sebasack/v-plotter/circuitos/2240466265006.jpg

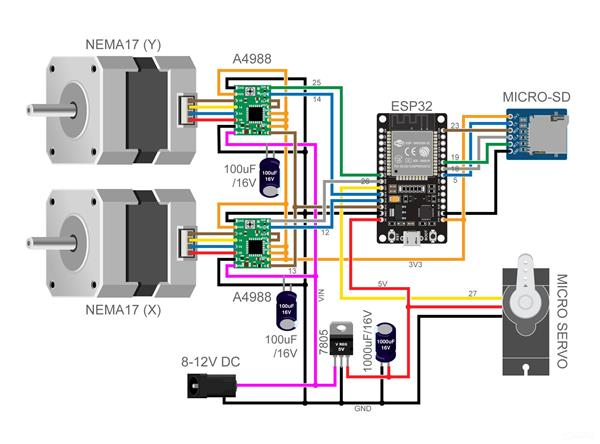
circuitos/2240466265006.jpg
