sebasack/v-plotter/circuitos/ESP32-interfacing-circuit-with-28BYJ-48-stepper-motor-and-uln2007.jpg

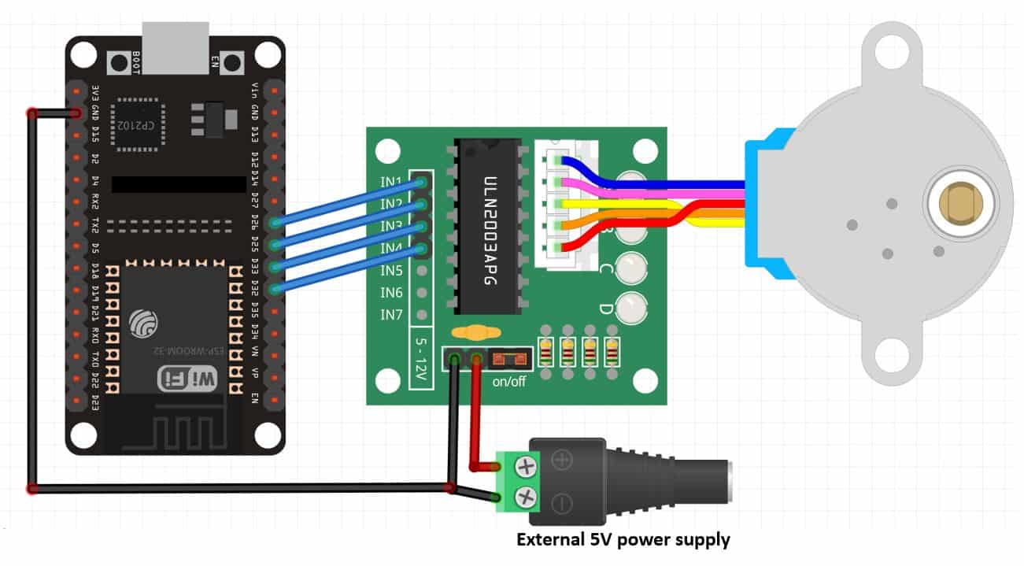
circuitos/ESP32-interfacing-circuit-with-28BYJ-48-stepper-motor-and-uln2007.jpg
