sebasack/v-plotter/convertir/pde/outline/outline_image.jpg

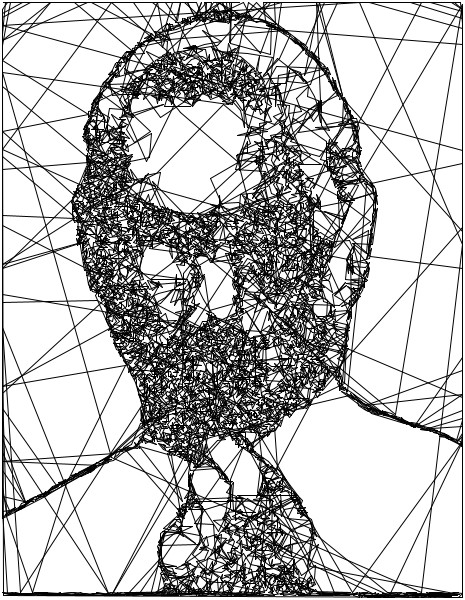
convertir/pde/outline/outline_image.jpg
