sebasack/v-plotter/hardware/mdf/Sde6bad2016fb44128df59bd70b1d3508Q.webp

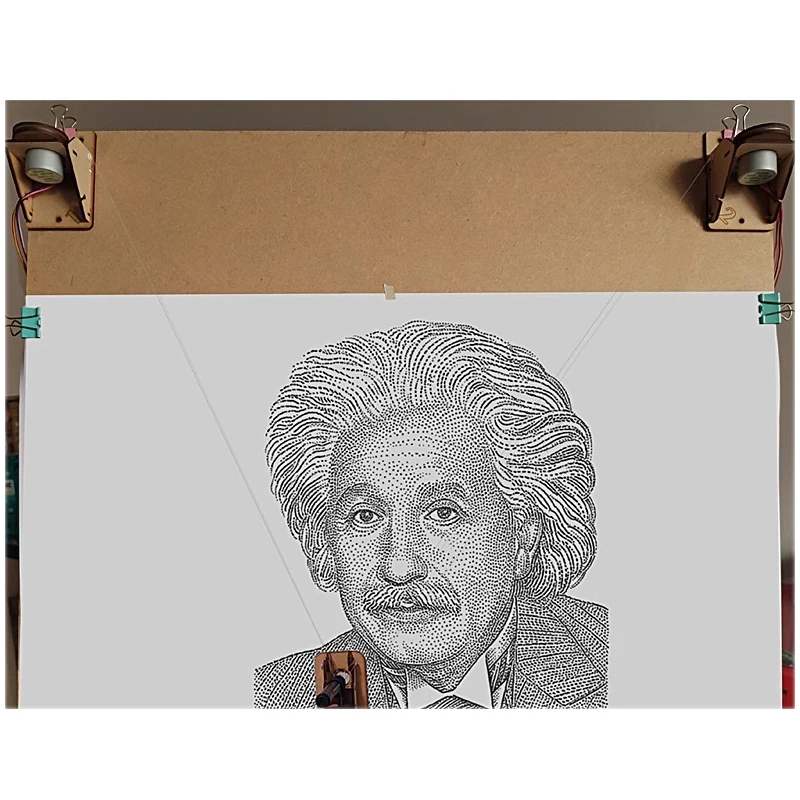
hardware/mdf/Sde6bad2016fb44128df59bd70b1d3508Q.webp
