sebasack/v-plotter/imagenes/bird.jpg

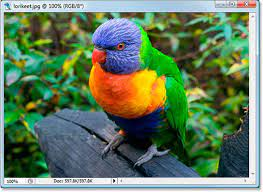
imagenes/bird.jpg
