sebasack/v-plotter/imagenes/casa.jpg

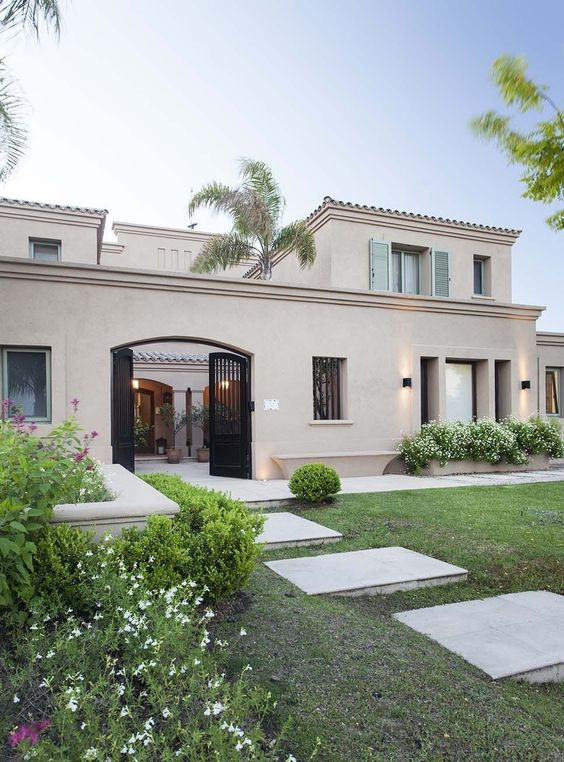
imagenes/casa.jpg
