sebasack/v-plotter/imagenes/cat.png

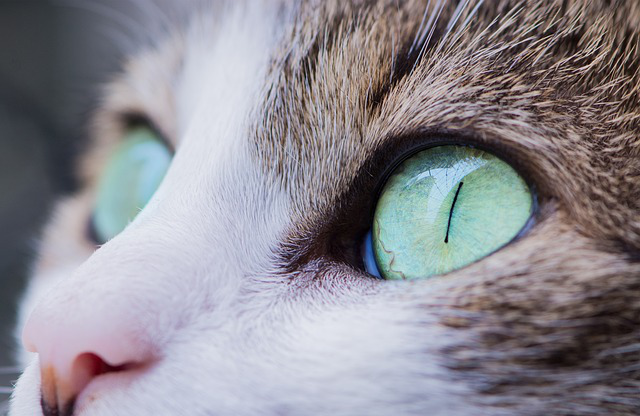
imagenes/cat.png
