sebasack/v-plotter/imagenes/dog.jpg

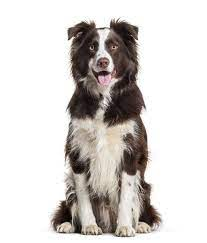
imagenes/dog.jpg
