sebasack/v-plotter/imagenes/escritorio.png

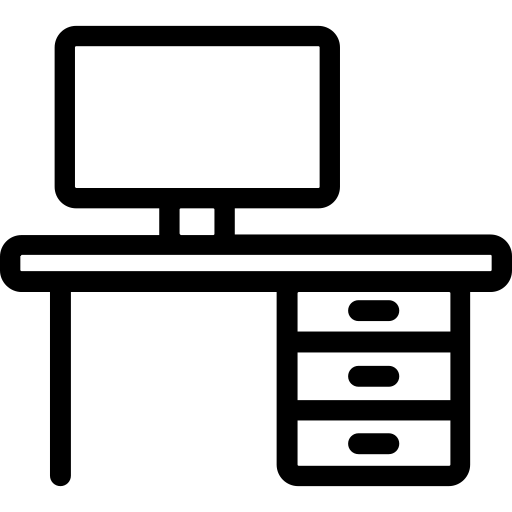
imagenes/escritorio.png
