sebasack/v-plotter/imagenes/figuras.webp

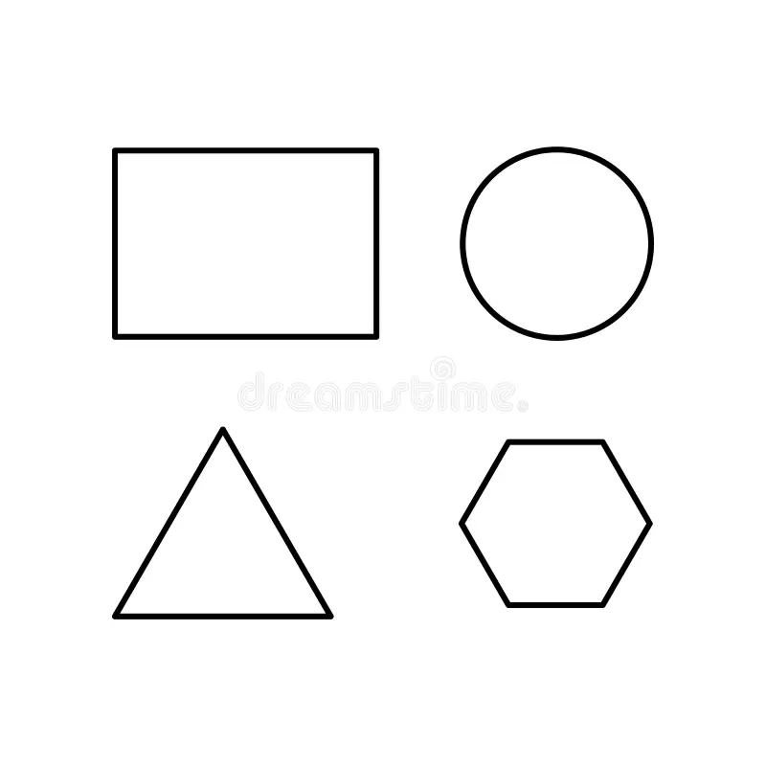
imagenes/figuras.webp
