sebasack/v-plotter/imagenes/jeep-wagoneer-2021.jpg

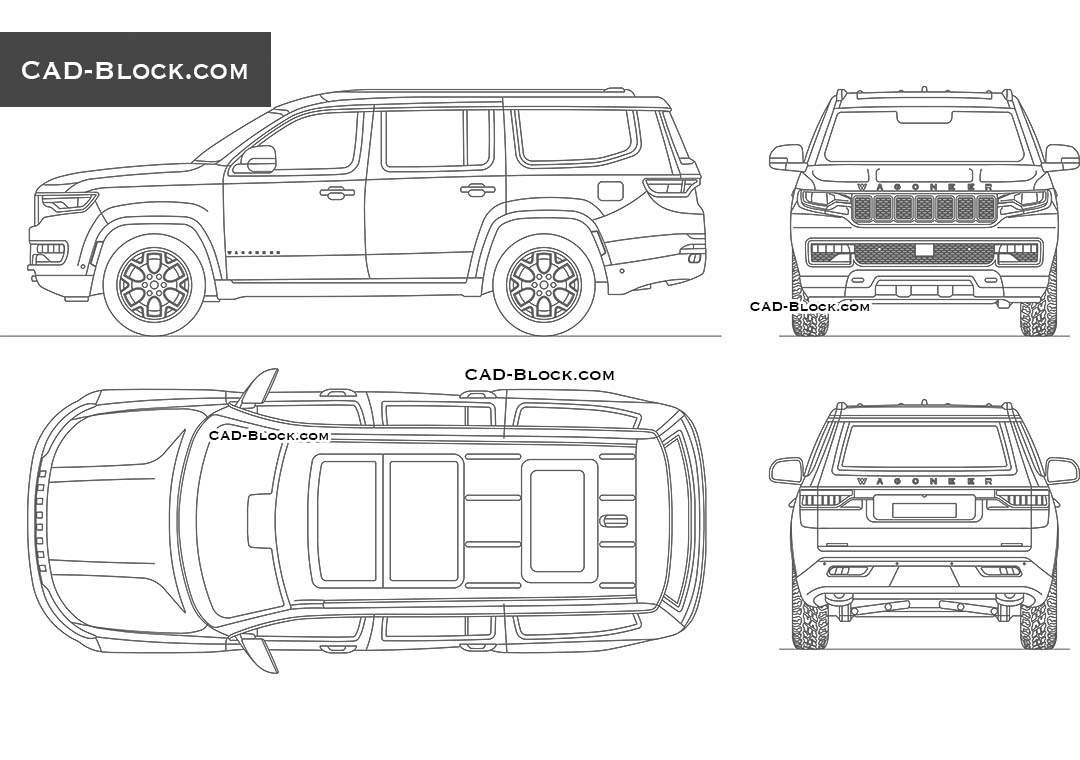
imagenes/jeep-wagoneer-2021.jpg
