sebasack/v-plotter/imagenes/manzana.jpg

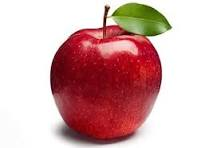
imagenes/manzana.jpg
