sebasack/v-plotter/imagenes/mariposa.jpg

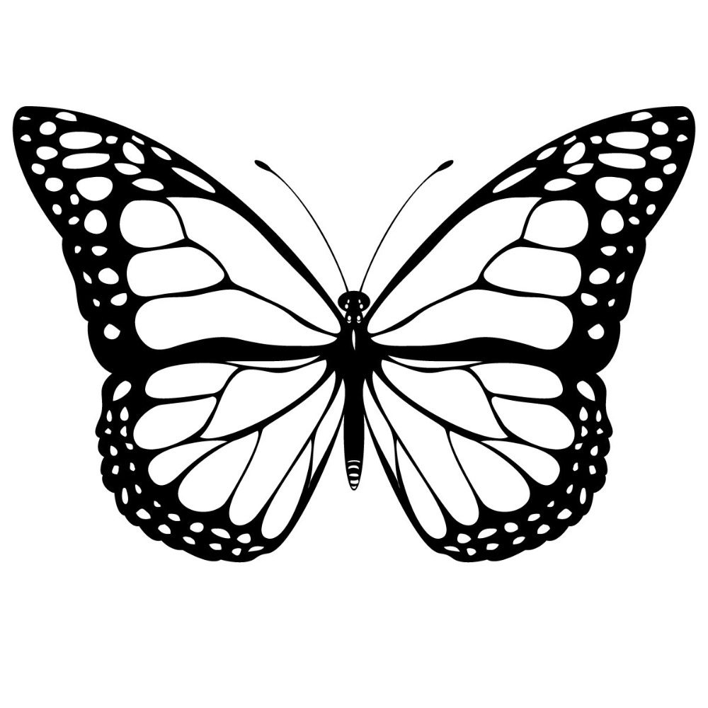
imagenes/mariposa.jpg
