sebasack/v-plotter/imagenes/mariposa_chica.jpg

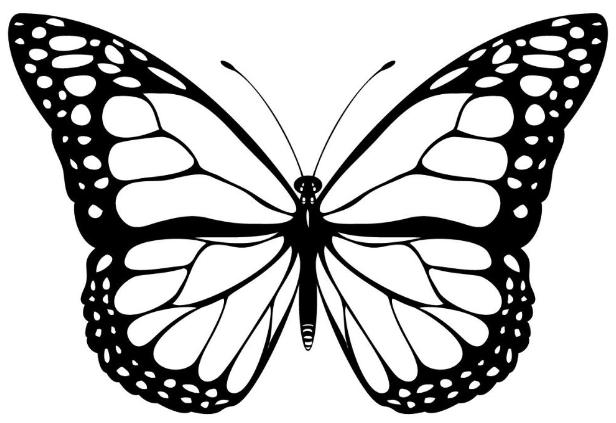
imagenes/mariposa_chica.jpg
