sebasack/v-plotter/imagenes/mariposa_inv.jpg

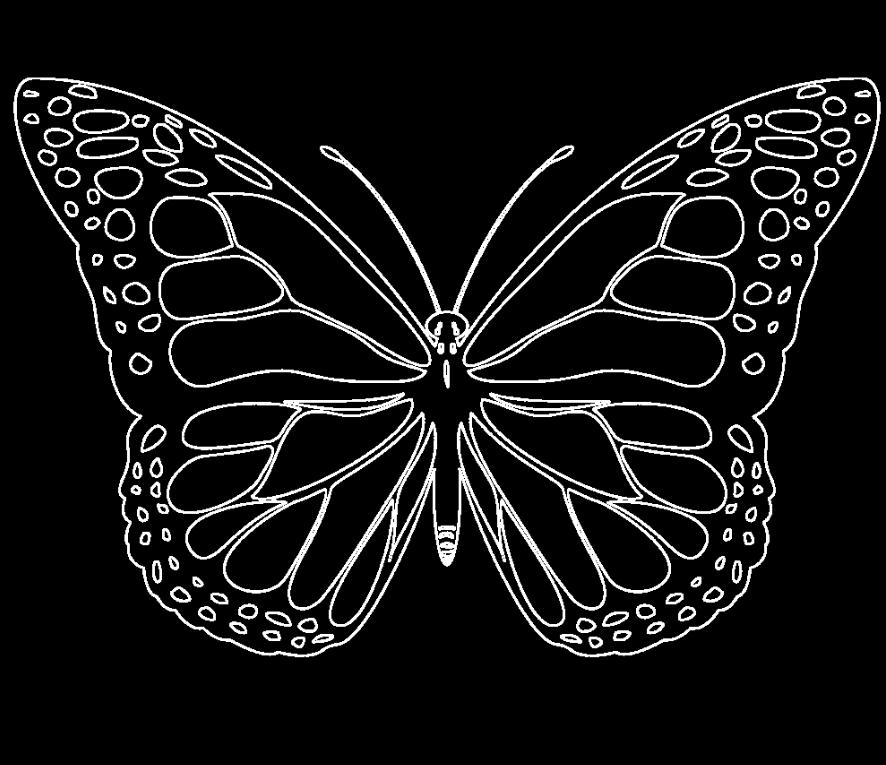
imagenes/mariposa_inv.jpg
