sebasack/v-plotter/imagenes/mariposas.jpg

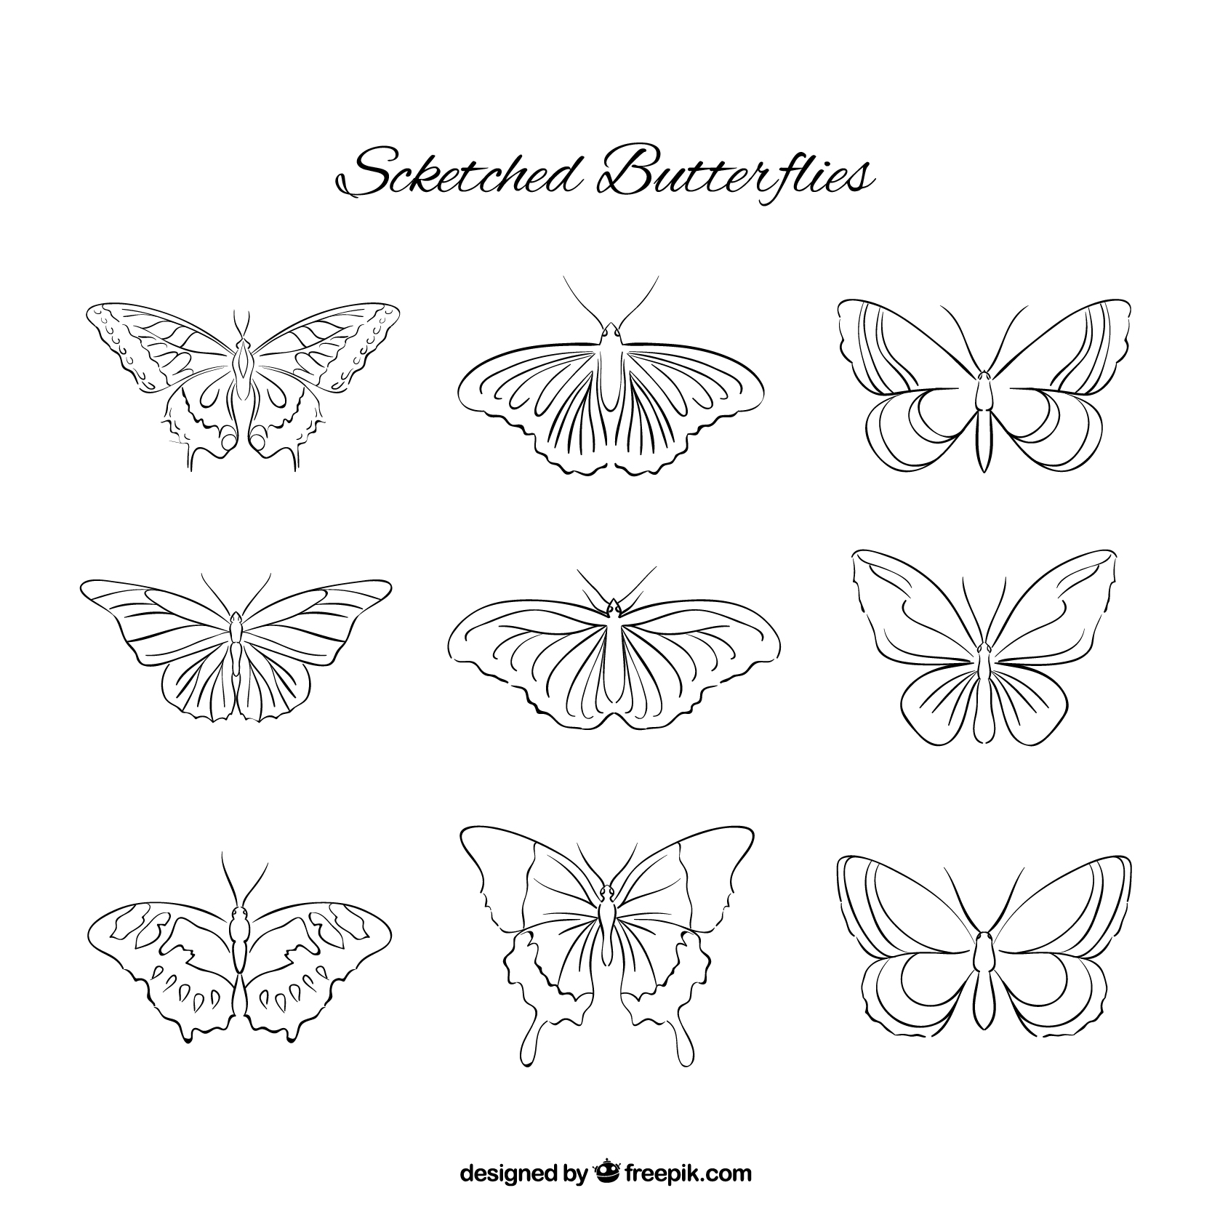
imagenes/mariposas.jpg
