sebasack/v-plotter/imagenes/nano-banana-2025-10-07T18-07-37.png

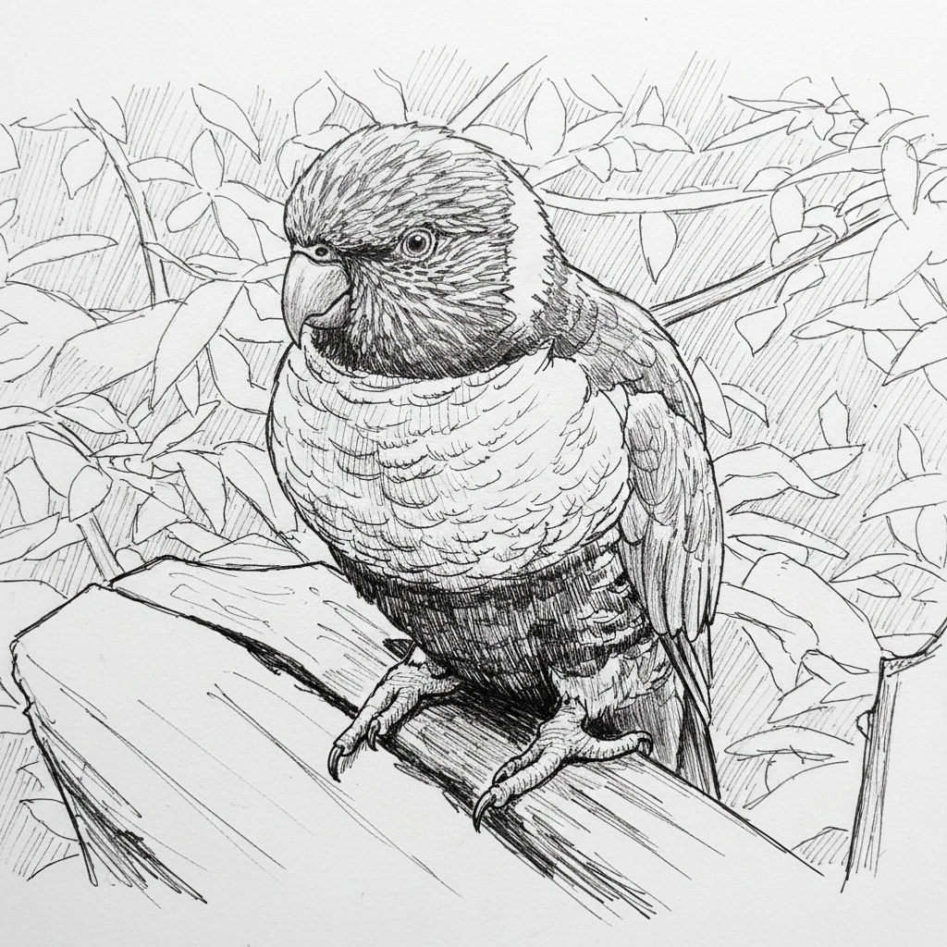
imagenes/nano-banana-2025-10-07T18-07-37.png
