sebasack/v-plotter/imagenes/perrito.jpg

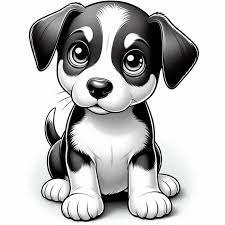
imagenes/perrito.jpg
