sebasack/v-plotter/imagenes/rgb-cmyk-modos-color.png

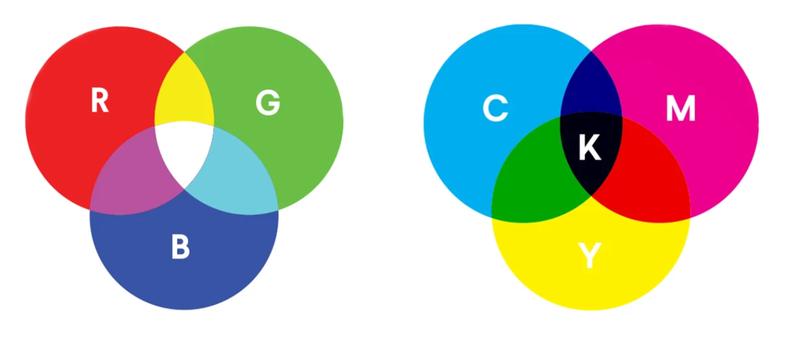
imagenes/rgb-cmyk-modos-color.png
