sebasack/v-plotter/SD/vPlotterMap.png

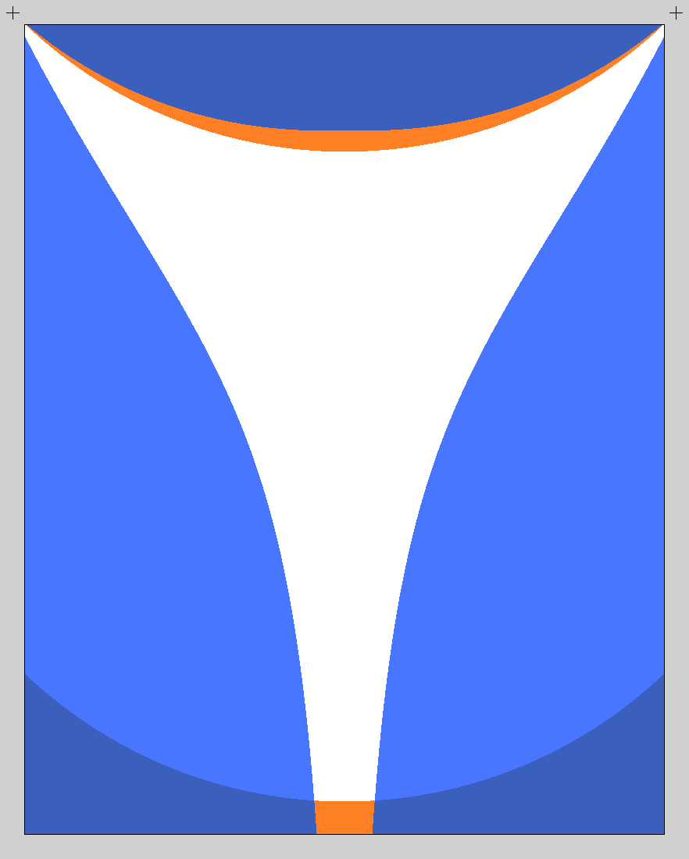
SD/vPlotterMap.png
