sebasack/v-plotter/v-plotter/util.ino

/**
*  Polargraph Server. - CORE
*  Written by Sandy Noble
*  Released under GNU License version 3.
*  http://www.polargraph.co.uk
*  https://github.com/euphy/polargraph_server_polarshield

Util.

This is one of the core files for the polargraph server program.

This has all the methods that let the rest actually work, including
the geometry routines that convert from the different coordinates
systems, and do transformations.
*/

static float translateX = 0.0;
static float translateY = 0.0;
static float scaleX = 1.0;
static float scaleY = 1.0;
static int rotateTransform = 0;

long multiplier(int in){
  return multiplier(long(in));
}

long multiplier(long in){
  return in * long(stepMultiplier);
}

float multiplier(double in){
  float out = in * (float) stepMultiplier;
  return out;
}

long divider(long in){
  return in / float(stepMultiplier);
}

void transform(long &tA, long &tB){

  tA = tA * scaleX;
  tB = tB * scaleY;

  // rotate

  if (rotateTransform >45 && rotateTransform <= 135){// 90 degree rotation
  
    float temp = tA;
    tA = -tB;
    tB = temp;
  } else if (rotateTransform > 135 && rotateTransform <= 225){// 180 degree rotation
  
    tA = -tA;
    tB = -tB;
  } else if (rotateTransform > 225 && rotateTransform <= 315){// 270 degree rotation
  
    float temp = tA;
    tA = tB;
    tB = -temp;
  } else {// no rotation  

  }

  tA = tA + translateX;
  tB = tB + translateY;

//  Serial.print("Out tA:");
//  Serial.println(tA);
//  Serial.print("Out tB:");
//  Serial.println(tB);

}

void changeLength(float tA, float tB){
  changeLength((long)tA, (long)tB);
}

void changeLength(long tA, long tB){
// Here. Finally. the motor moves.  CMD_CHANGELENGTHDIRECT = "C17" eventually gets here

  transform(tA,tB);

  float currSpeedA = motorA.speed();
  float currSpeedB = motorB.speed();

  // Serial.printf("A pos: %ld, A target: %ld\n", motorA.currentPosition(), tA);
  // Serial.printf("B pos: %ld, B target: %ld\n", motorB.currentPosition(), tB);


  motorA.setSpeed(0.0);
  motorB.setSpeed(0.0);
  motorA.moveTo(tA);
  motorB.moveTo(tB);

  if (!usingAcceleration)  {
    // The moveTo() function changes the speed in order to do a proper
    // acceleration. This counteracts it. Ha.
    
    if (motorA.speed() < 0){
      currSpeedA = -currSpeedA;
     } 
    if (motorB.speed() < 0){
      currSpeedB = -currSpeedB;
      }

  //  Serial.printf("Setting A speed (%ld) back to %ld\n", motorA.speed(), currSpeedA);
  //  Serial.printf("Setting B speed (%ld) back to %ld\n", motorB.speed(), currSpeedB);
      
    motorA.setSpeed(currSpeedA);
    motorB.setSpeed(currSpeedB);
  }
  
  
  while (motorA.distanceToGo() != 0 || motorB.distanceToGo() != 0){
    // seemed like a good idea?  This loop will take some time to run...
    // no, not really
    // taskYIELD();

    // the motor moves here

//    Serial.print("dA:");
//    Serial.print(motorA.distanceToGo());
//    Serial.print(", dB:");
//    Serial.println(motorB.distanceToGo());
    // impl_runBackgroundProcesses();
    if (currentlyRunning){
      if (usingAcceleration){
        motorA.run();
        motorB.run();
      } else {
       // Serial.println(motorA.speed());

        motorA.runSpeedToPosition();
        motorB.runSpeedToPosition();
      }


     //   Serial.print(" mueve motor 1");
    }
//    } else {
//      impl_runBackgroundProcesses();    // it's already running as a task, why call it again?
//    }


  }

  lastOperationTime = millis();
  //reportPosition();
}

void changeLengthRelative(float tA, float tB){
  changeLengthRelative((long) tA, (long)tB);
}

void changeLengthRelative(long tA, long tB){
  motorA.move(tA);
  motorB.move(tB);

  while (motorA.distanceToGo() != 0 || motorB.distanceToGo() != 0)  {
    //impl_runBackgroundProcesses();
    if (currentlyRunning)    {
      if (usingAcceleration)      {
        motorA.run();
        motorB.run();
      } else      {
        motorA.runSpeedToPosition();
        motorB.runSpeedToPosition();
      }


     //   Serial.print(" mueve motor 2");
    }
//    else {
//      impl_runBackgroundProcesses();  // it's already running as a task, why call it again?
//    }    
  }
  
  lastOperationTime = millis();
  //reportPosition();
}

void recalculateMachineSizeInSteps(){
  machineSizeSteps.x = machineSizeMm.x * stepsPerMm;
  machineSizeSteps.y = machineSizeMm.y * stepsPerMm;

  roveAreaSteps.pos.x = roveAreaMm.pos.x * stepsPerMm;
  roveAreaSteps.pos.y = roveAreaMm.pos.y * stepsPerMm;
  roveAreaSteps.size.x = roveAreaMm.size.x * stepsPerMm;
  roveAreaSteps.size.y = roveAreaMm.size.y * stepsPerMm;
}

void recalculateStepsPerMm(){
  mmPerStep = mmPerRev / multiplier(motorStepsPerRev);
  stepsPerMm = multiplier(motorStepsPerRev) / mmPerRev;
}

long getMaxLength(){
    if (maxLength == 0)  {
    float length = getMachineA(machineSizeSteps.x, machineSizeSteps.y);
    maxLength = long(length+0.5);
    Serial.print("Calculated maxLength: ");
    Serial.println(maxLength);
  }
  return maxLength;
}


float getMachineA(float cX, float cY){
  float a = sqrt(sq(cX)+sq(cY));
  return a;
}

float getMachineB(float cX, float cY){
  float b = sqrt(sq((machineSizeSteps.x)-cX)+sq(cY));
  return b;
}

void moveA(int dist){
  motorA.move(dist);
  while (motorA.distanceToGo() != 0)  {
    // impl_runBackgroundProcesses();
    if (currentlyRunning){
      motorA.run();
    }
       // Serial.print("  3");
  }
  lastOperationTime = millis();
}

void moveB(int dist){
  motorB.move(dist);
  while (motorB.distanceToGo() != 0)  {
    // impl_runBackgroundProcesses();
    if (currentlyRunning){
      motorB.run();
  }

    //    Serial.print(" mueve motor 4");
  }
  lastOperationTime = millis();
}

void reportPosition(){
  if (reportingPosition)  {

    
    PGclient.print(OUT_CMD_SYNC_STR);
    PGclient.print(divider(motorA.currentPosition()));
    PGclient.print(COMMA);
    PGclient.print(divider(motorB.currentPosition()));
    PGclient.println(CMD_END);


    Serial.print("    envio sync: ");
    Serial.print(OUT_CMD_SYNC_STR);
    Serial.print(divider(motorA.currentPosition()));
    Serial.print(COMMA);
    Serial.print(divider(motorB.currentPosition()));
    Serial.println(CMD_END);


    int cX = getCartesianX();
    int cY = getCartesianY(cX, motorA.currentPosition());
    Serial.print("     cartesian sync: ");
    Serial.print(cX*mmPerStep);
    Serial.print(COMMA);
    Serial.print(cY*mmPerStep);
    Serial.print(CMD_END);

  }
}

void reportStepRate(){
  #ifdef DEBUG_STEPRATE
  Serial.printf("Step frequencies: %ld (%ld stepped), %ld(%ld stepped), %ld(%ld stepped), total: %ld in %ld seconds.\n",
    sampleBuffer[0],
    steppedBuffer[0],
    sampleBuffer[1],
    steppedBuffer[1],
    sampleBuffer[2],
    steppedBuffer[2],
    totalTriggers,
    totalSamplePeriods);
  #endif
}



void engageMotors(){
  impl_engageMotors();
}

void releaseMotors(){
  impl_releaseMotors();
}


float getCartesianXFP(float aPos, float bPos){
//  Serial.print("aPos: ");
//  Serial.print(aPos);
//  Serial.print(" bPos: ");
//  Serial.print(bPos);
//  Serial.print(" machineSizeSteps.x ");
//  Serial.println(machineSizeSteps.x);
//
//  Serial.print("Float calc: sq aPos: ");
//  Serial.print(sq(aPos));
//  Serial.print(" bPos: ");
//  Serial.print(sq(bPos));
//  Serial.print(" machineSizeSteps.x*2 ");
//  Serial.print((float)machineSizeSteps.x * 2.0);
//  Serial.print(" machineSizeSteps.x sq ");
//  Serial.println(sq((float)machineSizeSteps.x));
//
//  Serial.print("Int calc: sq aPos: ");
//  Serial.print(sq(aPos));
//  Serial.print(" bPos: ");
//  Serial.print(sq(bPos));
//  Serial.print(" machineSizeSteps.x*2 ");
//  Serial.print(machineSizeSteps.x * 2.0);
//  Serial.print(" machineSizeSteps.x sq ");
//  Serial.println(sq(machineSizeSteps.x));

  float calcX = (sq((float)machineSizeSteps.x) - sq((float)bPos) + sq((float)aPos)) / ((long) machineSizeSteps.x * 2.0);

//  Serial.print("CalcX float: ");
//  Serial.println(calcX);

  return calcX;
}

float getCartesianYFP(float cX, float aPos){
//  Serial.print("aPos: ");
//  Serial.print(aPos);
//  Serial.print(" cx: ");
//  Serial.println(cX);
//
//  Serial.print("sq aPos: ");
//  Serial.print(sq(aPos));
//  Serial.print(" cx: ");
//  Serial.println(sq(cX));

  float calcY = sqrt(sq(aPos)-sq(cX));
//  Serial.print("CalcY: ");
//  Serial.println(calcY);
  return calcY;
}

long getCartesianX(float aPos, float bPos){
  long calcX = long((pow(machineSizeSteps.x, 2) - pow(bPos, 2) + pow(aPos, 2)) / (machineSizeSteps.x*2));
  return calcX;
}

long getCartesianX(){
  long calcX = getCartesianX(motorA.currentPosition(), motorB.currentPosition());
  return calcX;
}

long getCartesianY(){
  return getCartesianY(getCartesianX(), motorA.currentPosition());
}

long getCartesianY(long cX, float aPos){
  long calcY = long(sqrt(pow(aPos,2)-pow(cX,2)));
  return calcY;
}
